mariusmym/LedClock-Resized/LedClock-Resized2-40x66mm/CAD_Files/LedClock-Resized2-40x66mm v2.png

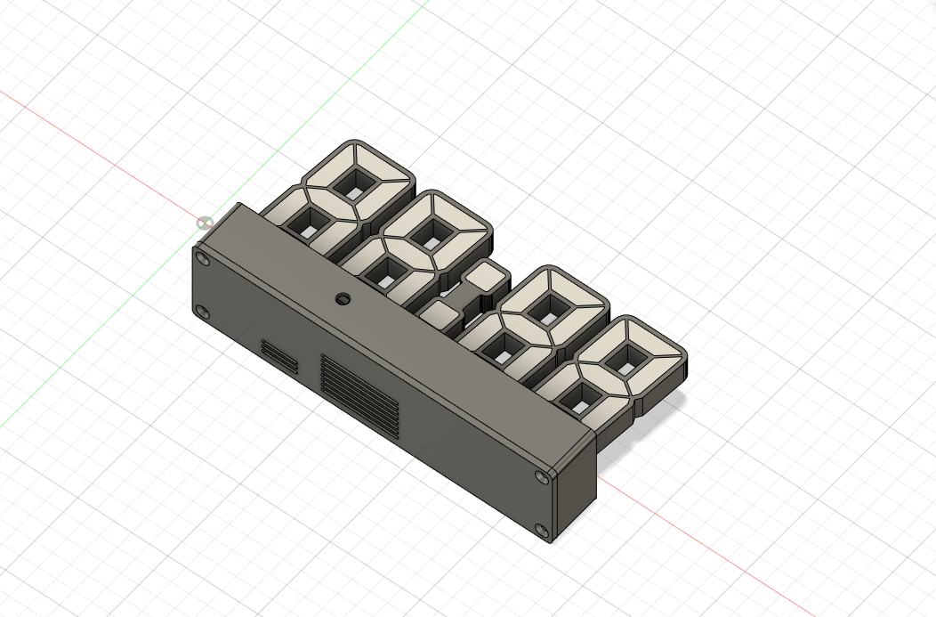
LedClock-Resized2-40x66mm/CAD_Files/LedClock-Resized2-40x66mm v2.png
