mariusmym/LedClock-Resized/LedClock-Resized2-40x66mm/Images/IMG_4708.jpeg

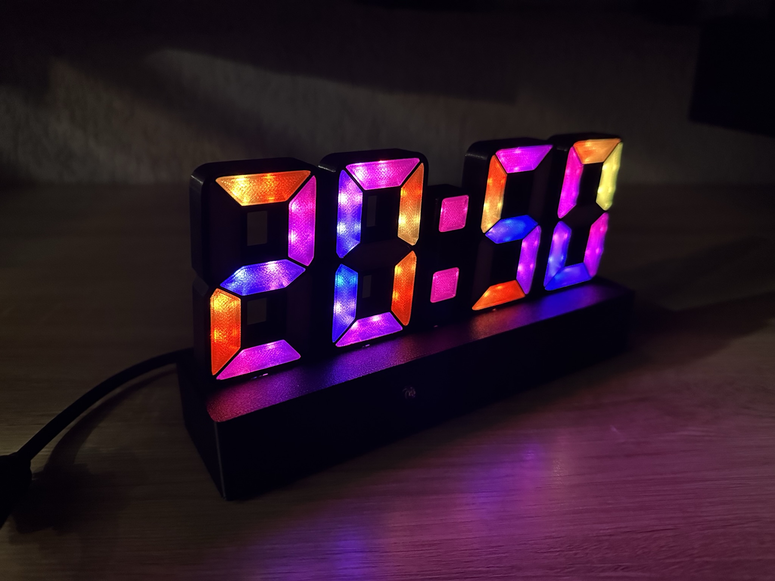
LedClock-Resized2-40x66mm/Images/IMG_4708.jpeg
