mariusmym/LedClock-Resized/LedClock-Resized2-40x66mm/Gerber_files_and_BOM/7SEG_40X66_2.png

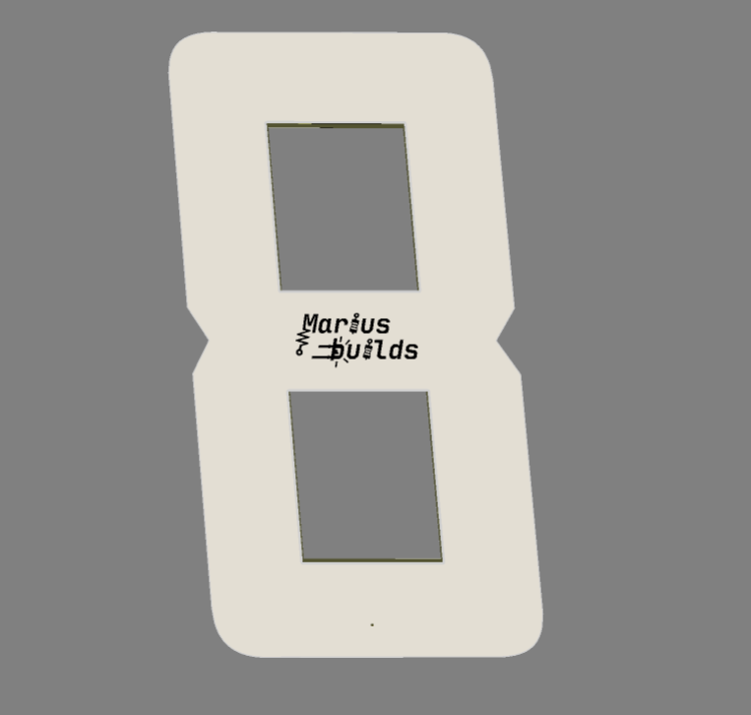
LedClock-Resized2-40x66mm/Gerber_files_and_BOM/7SEG_40X66_2.png
