mariusmym/LedClock-Resized/LedClock-Resized2-40x66mm/Gerber_files_and_BOM/7SEG_DOTS_40X66_1.png

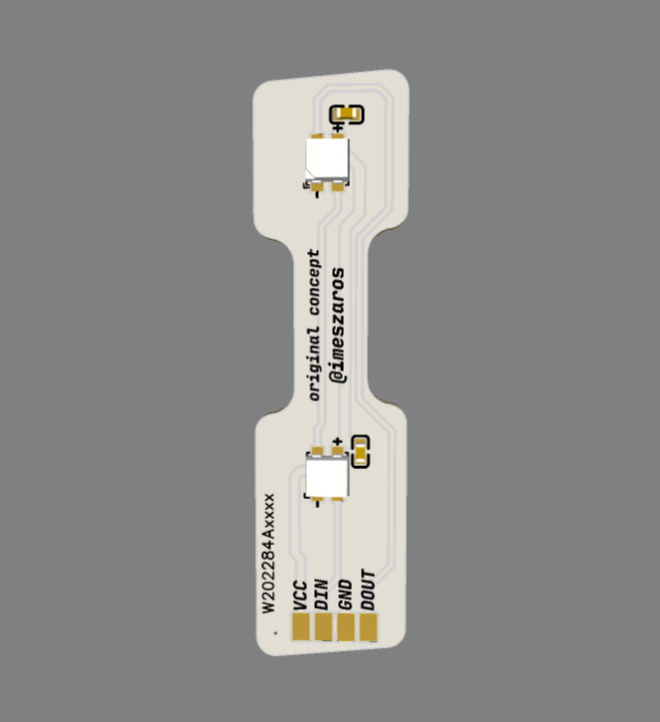
LedClock-Resized2-40x66mm/Gerber_files_and_BOM/7SEG_DOTS_40X66_1.png
