mariusmym/LedClock-Resized/LedClock-Resized2-40x66mm/Gerber_files_and_BOM/LED_Clock_Board-ESP32-D1-MINI_2.png

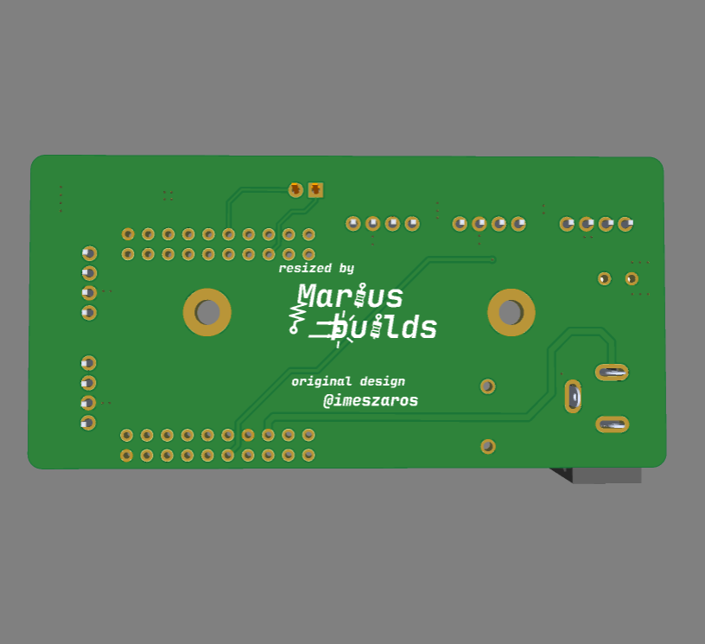
LedClock-Resized2-40x66mm/Gerber_files_and_BOM/LED_Clock_Board-ESP32-D1-MINI_2.png
