mariusmym/LedClock-Resized/LedClock_Resized/Gerber-Files_and_BOM/LED_Clock_Resized_7Segment_2.png

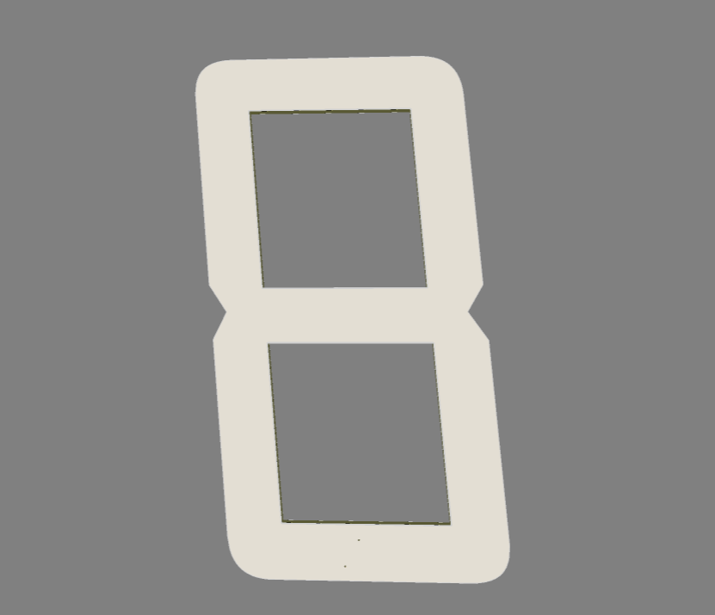
LedClock_Resized/Gerber-Files_and_BOM/LED_Clock_Resized_7Segment_2.png
