mariusmym/LedClock-Resized/LedClock-Resized2-40x66mm/3D_printing_files/3mf_files/7SEG_DOTS_LED_Covers.3mf

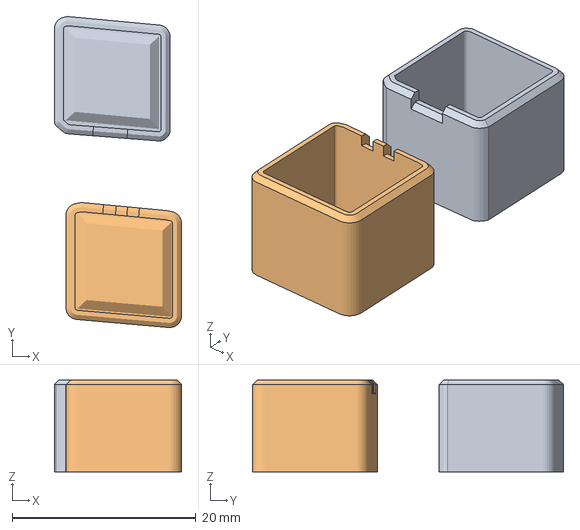
[picture p28: CAD file, 2023-03-20]
LedClock-Resized2-40x66mm/3D_printing_files/3mf_files/7SEG_DOTS_LED_Covers.3mf
13.9 x 33.8 x 10.0 mm
DotsCover1.stl
DotsCover2.stl
