mariusmym/LedClock-Resized/LedClock-Resized2-40x66mm/3D_printing_files/STL_files/7SEG_40x66/SegCovBody5.stl

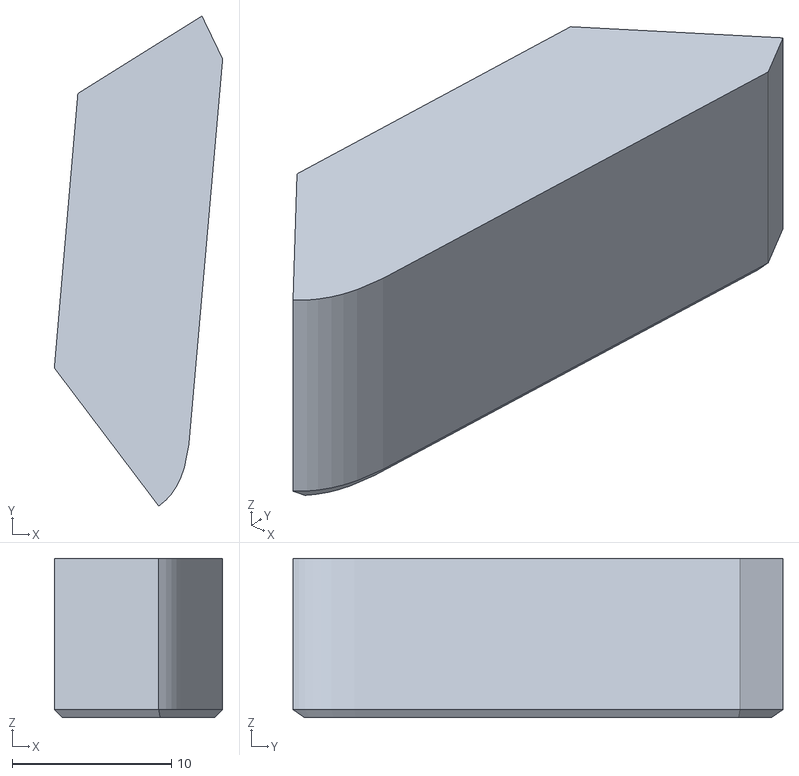
[picture p29: CAD file, 2023-03-20]
LedClock-Resized2-40x66mm/3D_printing_files/STL_files/7SEG_40x66/SegCovBody5.stl
10.6 x 30.8 x 10.0
