mariusmym/LedClock-Resized/LedClock_Resized/3D-print/3mf-files/CE3_SegmentCase.3mf

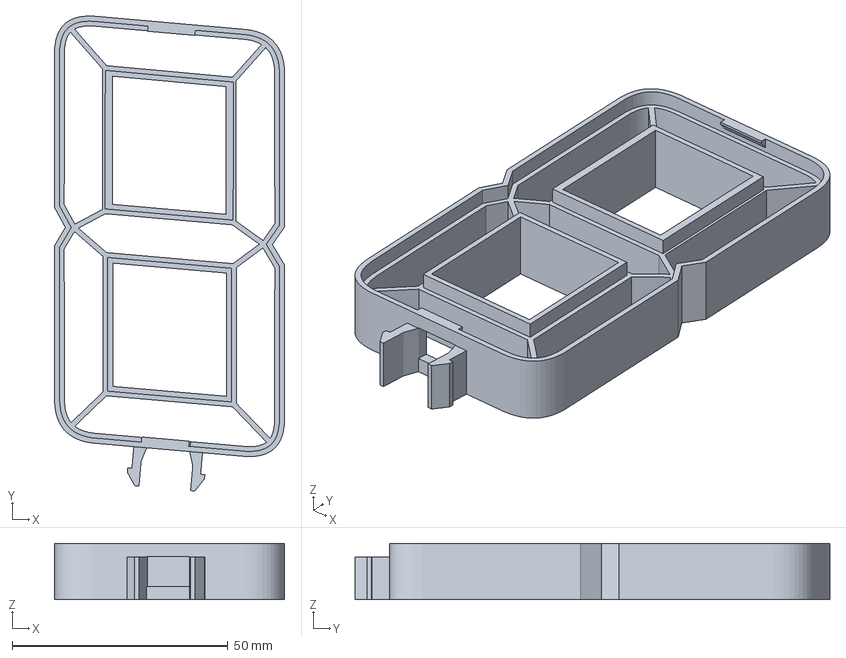
[picture p30: CAD file, 2023-03-15]
LedClock_Resized/3D-print/3mf-files/CE3_SegmentCase.3mf
53.4 x 110.1 x 13.0 mm
