mariusmym/LedClock-Resized/LedClock_Resized/3D-print/stl-files/SegmentCover-Bottom.stl

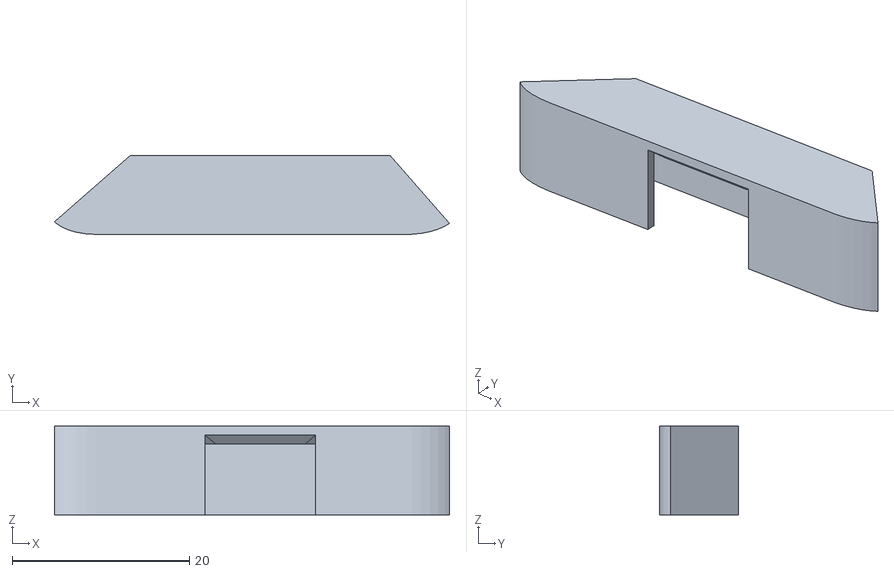
[picture p31: CAD file, 2023-03-15]
LedClock_Resized/3D-print/stl-files/SegmentCover-Bottom.stl
44.6 x 8.91 x 10.0
