mariusmym/LedClock-Resized/LedClock-Resized2-40x66mm/3D_printing_files/3mf_files/7SEG_CASE_40x66.3mf

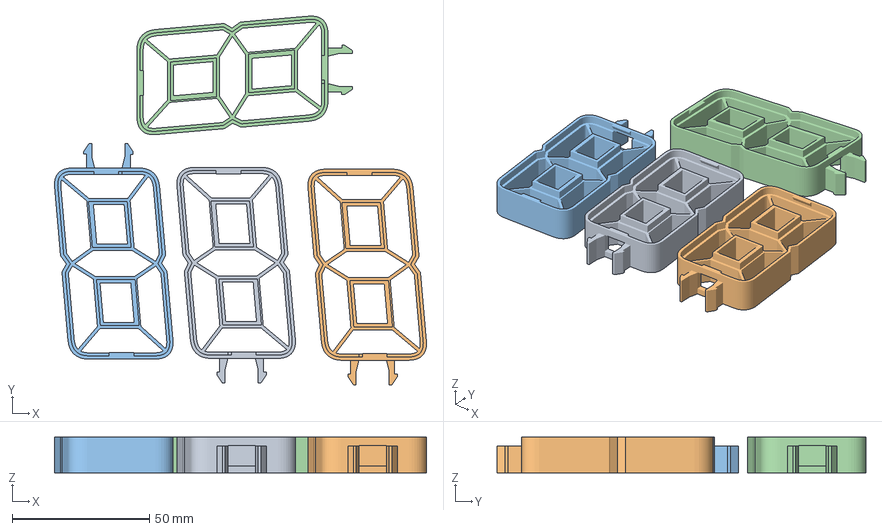
[picture p32: CAD file, 2023-03-20]
LedClock-Resized2-40x66mm/3D_printing_files/3mf_files/7SEG_CASE_40x66.3mf
135.5 x 134.4 x 13.0 mm
Case.stl
Case.stl(1)
Case.stl(2)
Case.stl(3)
