mariusmym/LedClock-Resized/LedClock_Resized/3D-print/stl-files/Dots-Case.stl

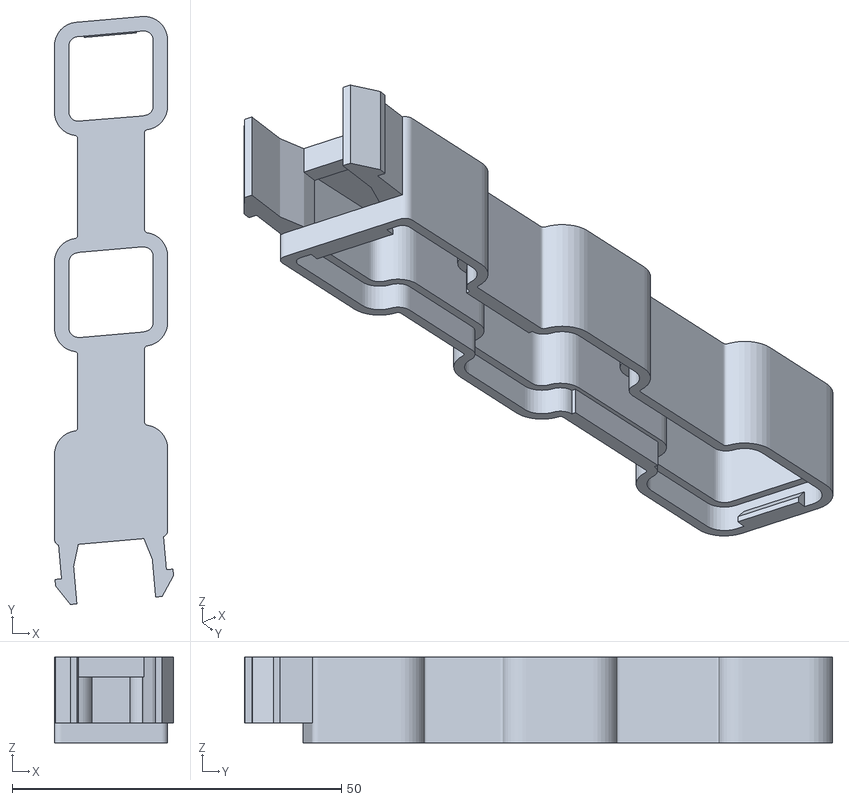
[picture p34: CAD file, 2023-03-15]
LedClock_Resized/3D-print/stl-files/Dots-Case.stl
18.1 x 89.3 x 13.0
