mariusmym/LedClock-Resized/LedClock-Resized2-40x66mm/3D_printing_files/STL_files/7SEG_40x66/SegCovBody2.stl

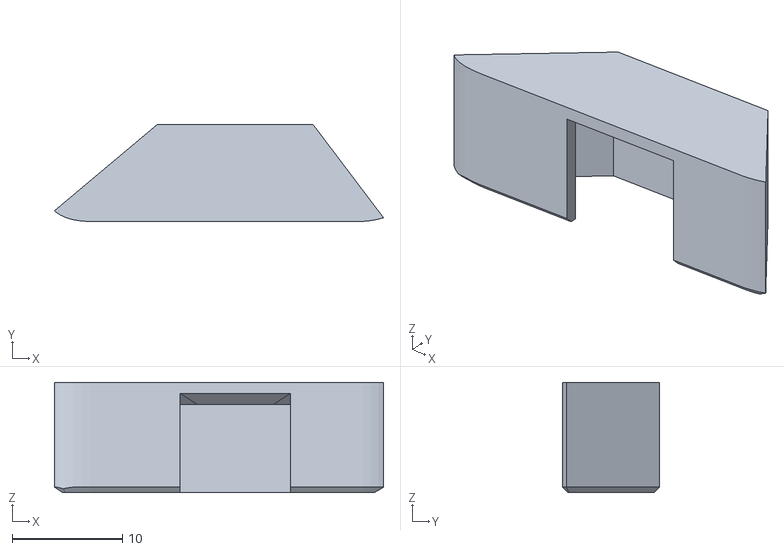
[picture p35: CAD file, 2023-03-20]
LedClock-Resized2-40x66mm/3D_printing_files/STL_files/7SEG_40x66/SegCovBody2.stl
29.8 x 8.79 x 10.0
