mariusmym/LedClock-Resized/LedClock-Resized2-40x66mm/3D_printing_files/STL_files/7SEG_40x66/SegCovBody7.stl

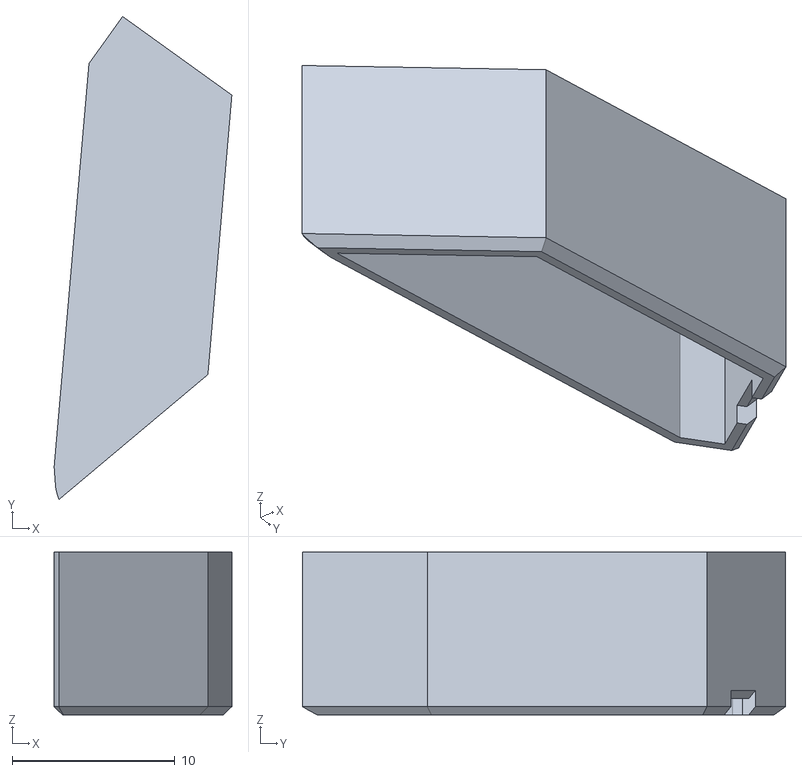
[picture p36: CAD file, 2023-03-20]
LedClock-Resized2-40x66mm/3D_printing_files/STL_files/7SEG_40x66/SegCovBody7.stl
10.9 x 29.7 x 10.0
