mariusmym/LedClock-Resized/LedClock_Resized/3D-print/stl-files/SegmentCover-Top.stl

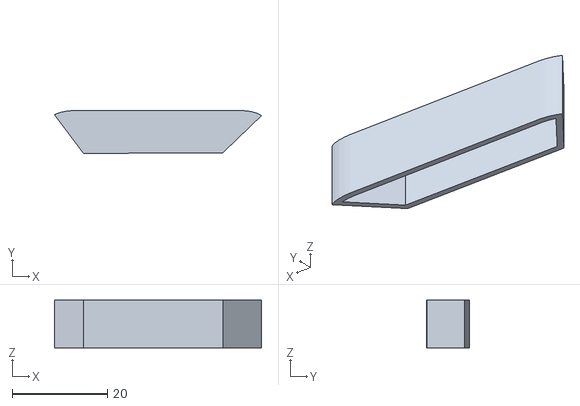
[picture p38: CAD file, 2023-03-15]
LedClock_Resized/3D-print/stl-files/SegmentCover-Top.stl
43.5 x 9.01 x 10.0
