mariusmym/LedClock-Resized/LedClock_Resized/3D-print/stl-files/SegmentCover-Center.stl

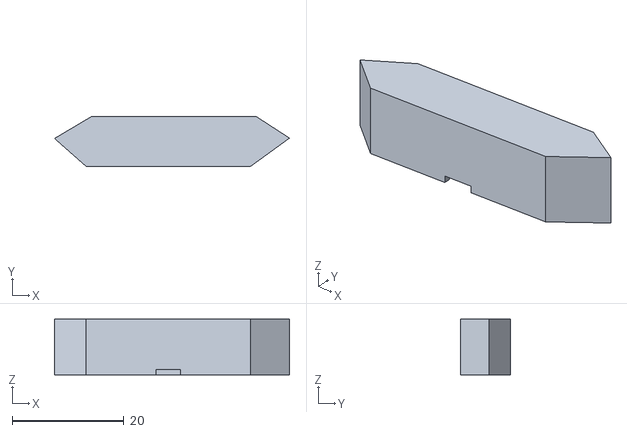
[picture p39: CAD file, 2023-03-15]
LedClock_Resized/3D-print/stl-files/SegmentCover-Center.stl
42.1 x 8.96 x 10.0
