mariusmym/LedClock-Resized/LedClock_Resized/3D-print/stl-files/SegmentCover-BottomLeft.stl

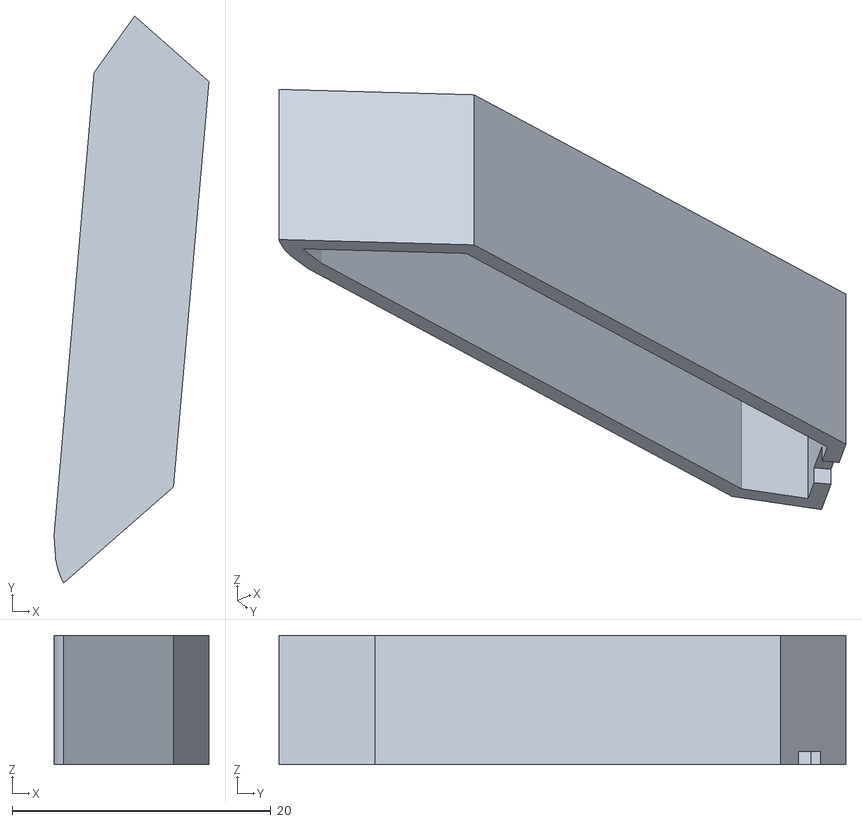
[picture p40: CAD file, 2023-03-15]
LedClock_Resized/3D-print/stl-files/SegmentCover-BottomLeft.stl
12.0 x 43.8 x 10.0
