mariusmym/LedClock-Resized/LedClock_Resized/3D-print/stl-files/BaseBodyB.stl

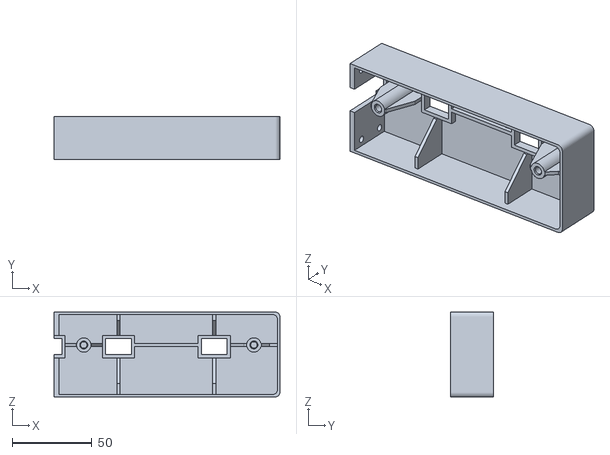
[picture p41: CAD file, 2023-03-15]
LedClock_Resized/3D-print/stl-files/BaseBodyB.stl
141.6 x 27.0 x 53.2
