mariusmym/LedClock-Resized/LedClock_Resized/3D-print/stl-files/Dots-LedCover-ALL.stl

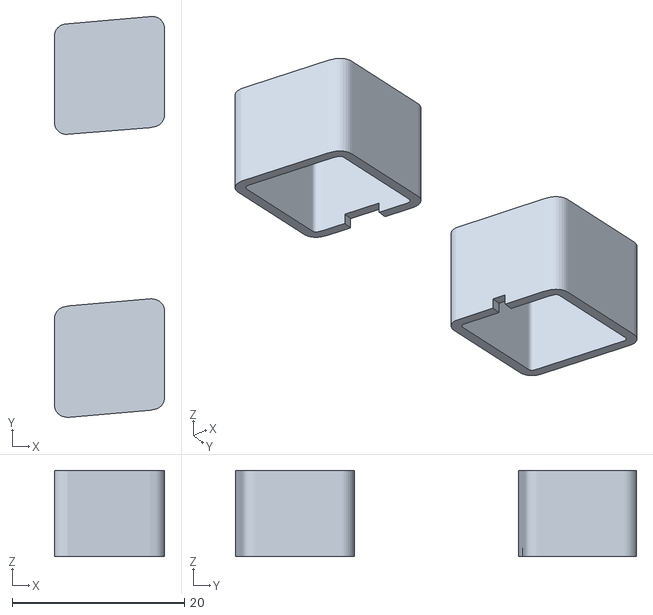
[picture p42: CAD file, 2023-03-15]
LedClock_Resized/3D-print/stl-files/Dots-LedCover-ALL.stl
12.8 x 46.6 x 10.0
