mariusmym/LedClock-Resized/LedClock_Resized/3D-print/stl-files/SegmentCase.stl

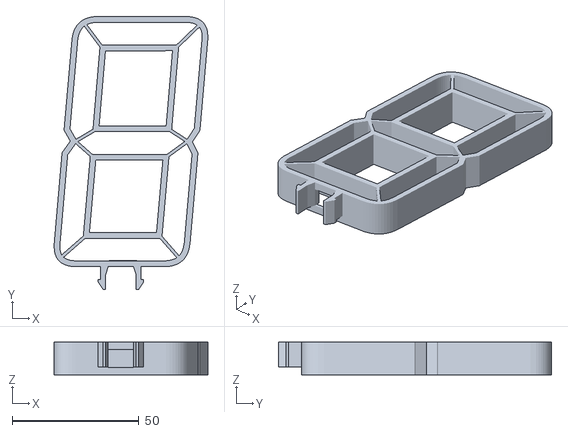
[picture p43: CAD file, 2023-03-15]
LedClock_Resized/3D-print/stl-files/SegmentCase.stl
60.7 x 107.6 x 13.0
