mariusmym/LedClock-Resized/LedClock_Resized/3D-print/stl-files/SegmentCover-TopLeft.stl

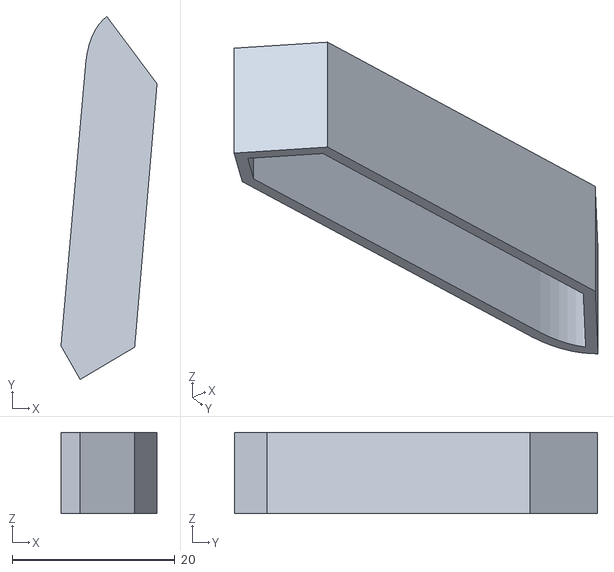
[picture p44: CAD file, 2023-03-15]
LedClock_Resized/3D-print/stl-files/SegmentCover-TopLeft.stl
11.8 x 44.6 x 10.0
