mariusmym/LedClock-Resized/LedClock_Resized/3D-print/stl-files/BaseLidA.stl

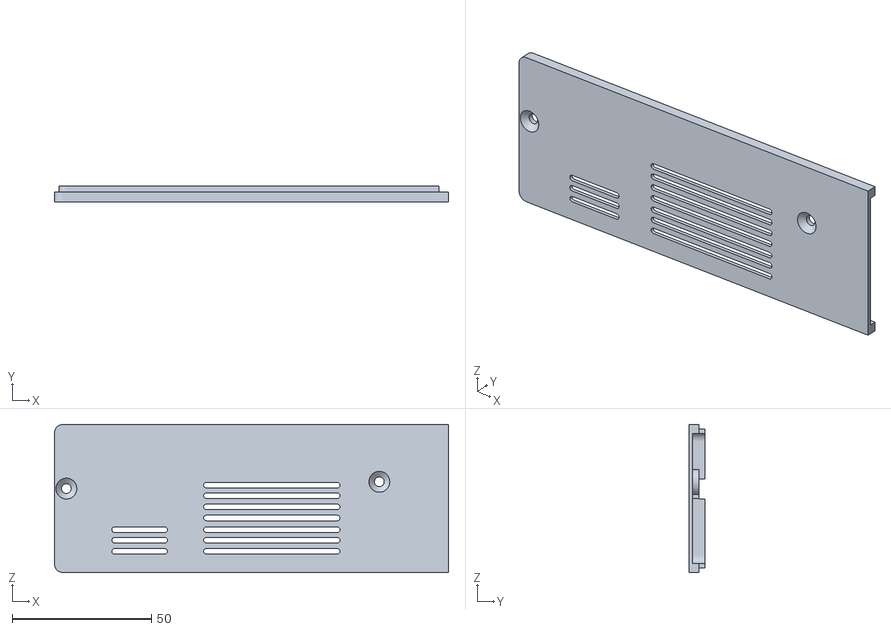
[picture p46: CAD file, 2023-03-15]
LedClock_Resized/3D-print/stl-files/BaseLidA.stl
141.6 x 5.60 x 53.2
